Apy985/Agua-0/hardware/esquematico.png

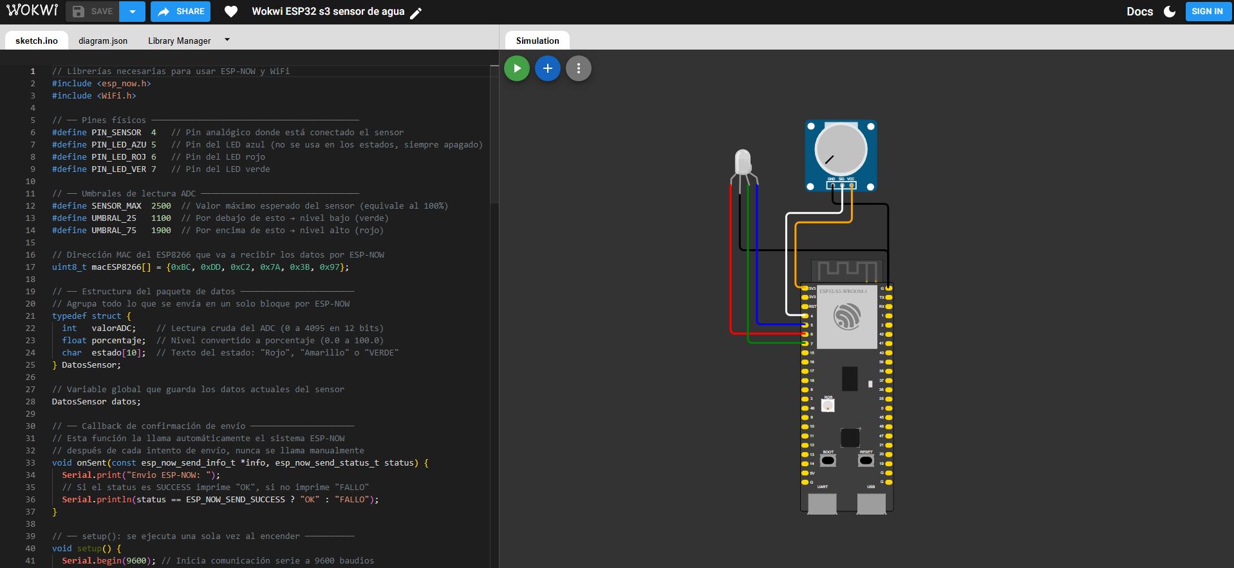
hardware/esquematico.png
