Apy985/Agua-0/hardware/fotos/imagen prototipo 1.jpg

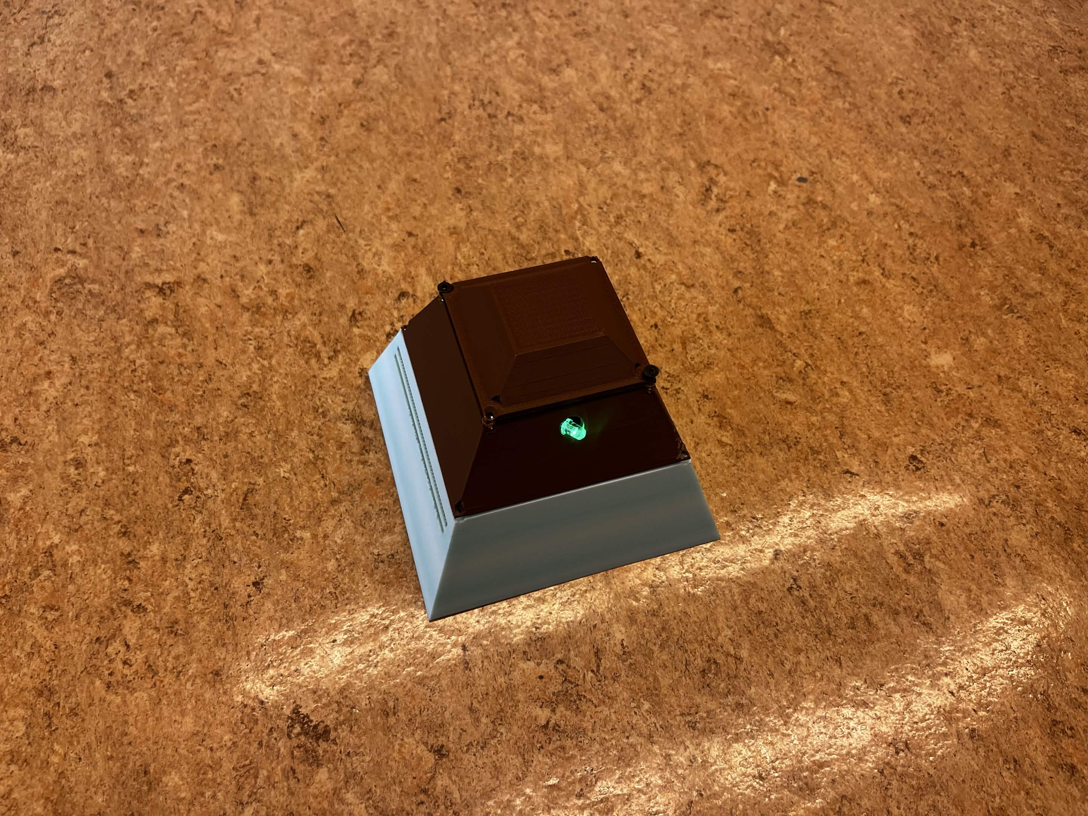
hardware/fotos/imagen prototipo 1.jpg
